Sancus11/RackGloves/images/IMG_20240603_130146942.jpg

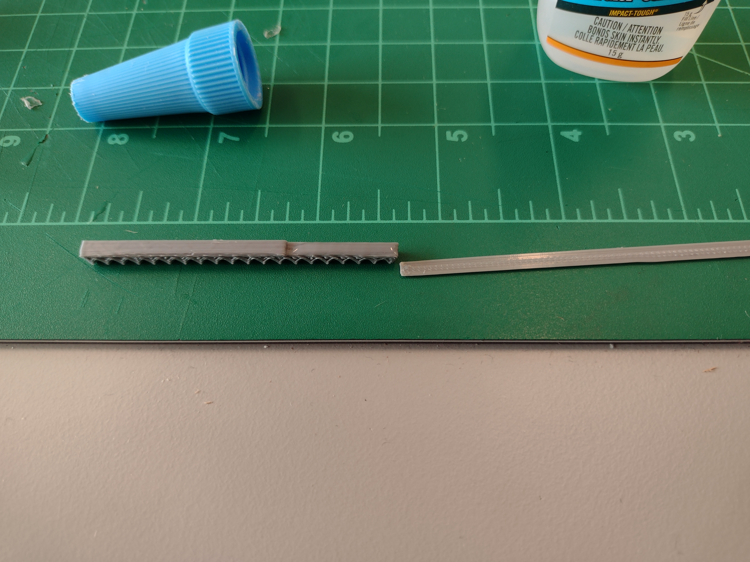
images/IMG_20240603_130146942.jpg
