Sancus11/RackGloves/images/IMG_20240604_150035656.jpg

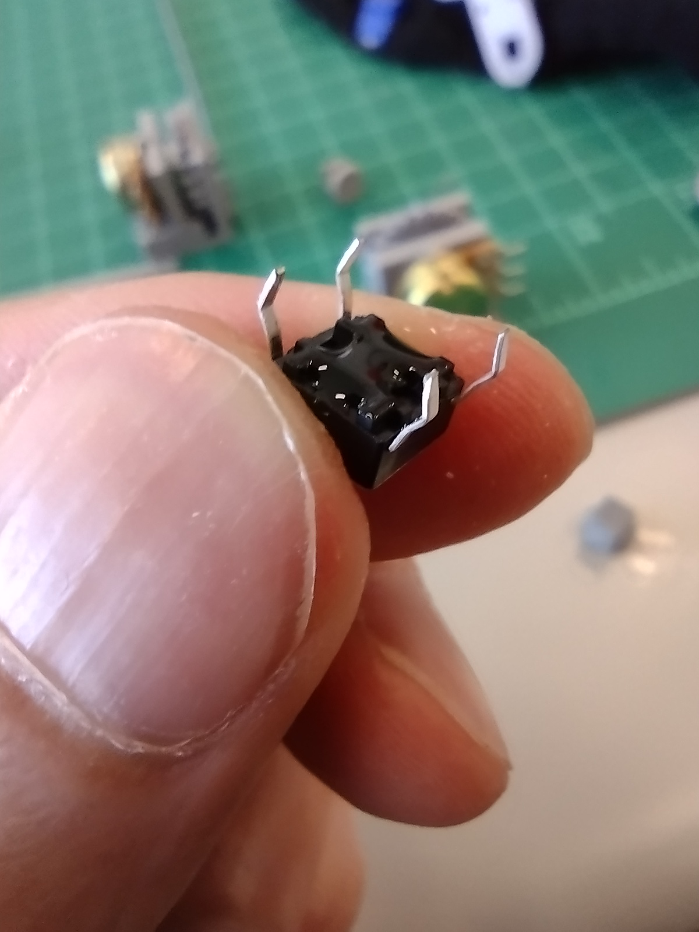
images/IMG_20240604_150035656.jpg
