Sancus11/RackGloves/images/IMG_20240606_152140470.jpg

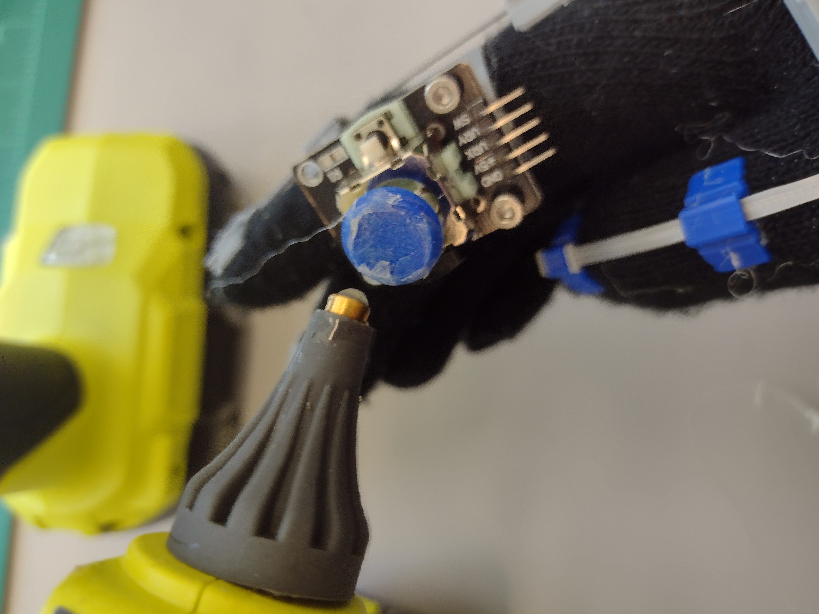
images/IMG_20240606_152140470.jpg
