Sancus11/RackGloves/everything v1/proto gloves/P-T-M-24-L.stl

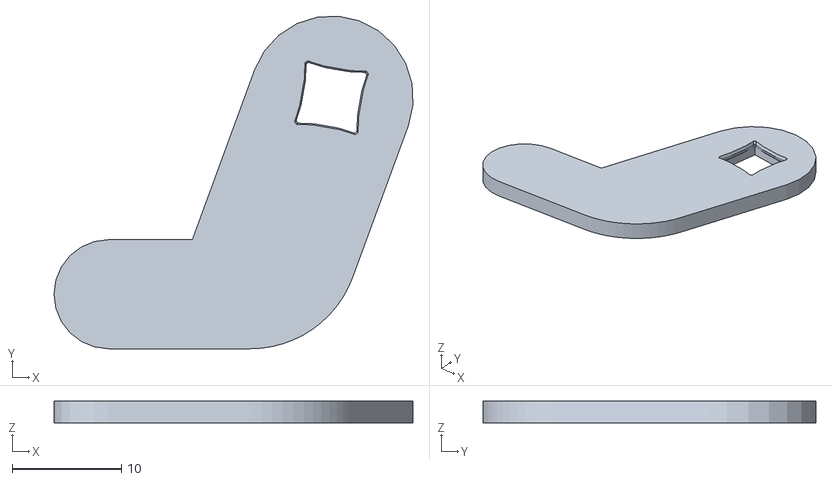
[picture p24: CAD file, 2024-06-14]
everything v1/proto gloves/P-T-M-24-L.stl
32.9 x 30.5 x 2.00
