Sancus11/RackGloves/everything v1/rack unit/spur gear.stl

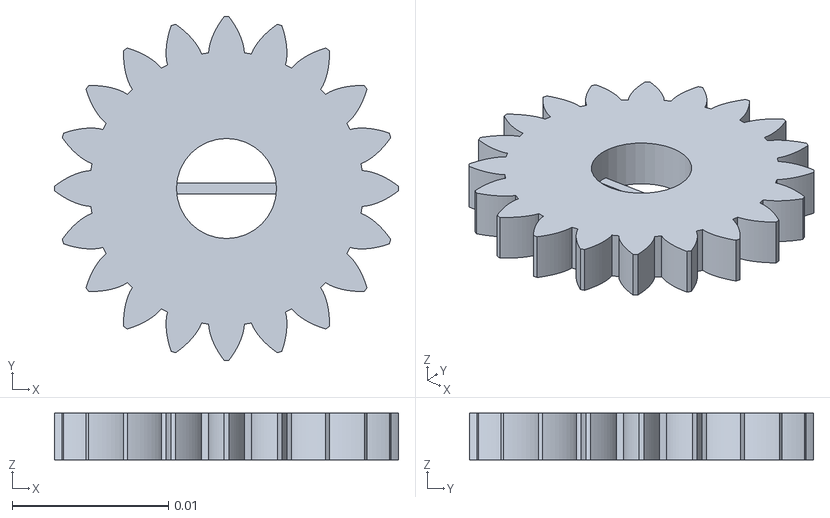
[picture p25: CAD file, 2024-06-14]
everything v1/rack unit/spur gear.stl
0.022 x 0.022 x 0.003
