Sancus11/RackGloves/everything v1/controlls/joystick nub.stl

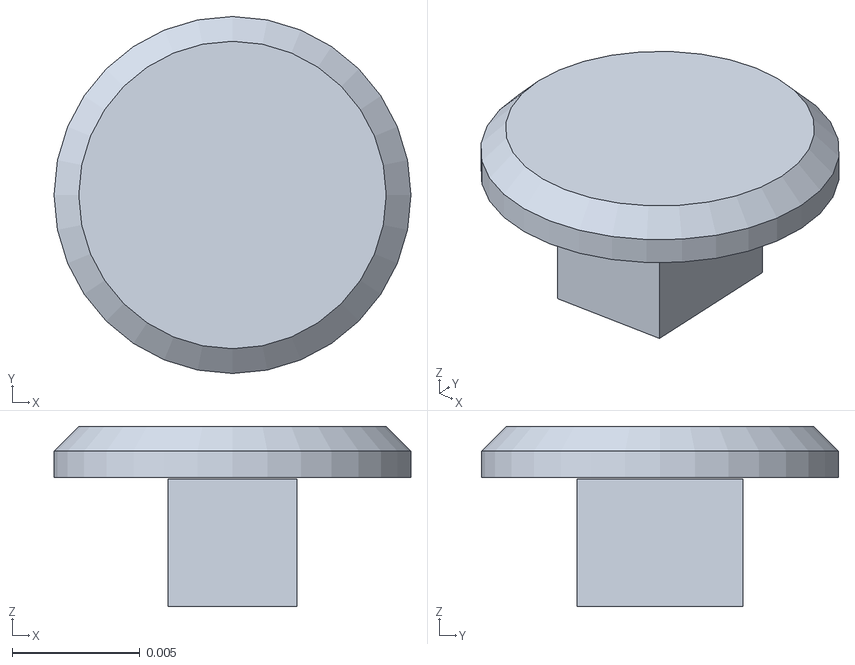
[picture p26: CAD file, 2024-06-14]
everything v1/controlls/joystick nub.stl
0.014 x 0.014 x 0.00707
