Sancus11/RackGloves/everything v1/espcase/button push.stl

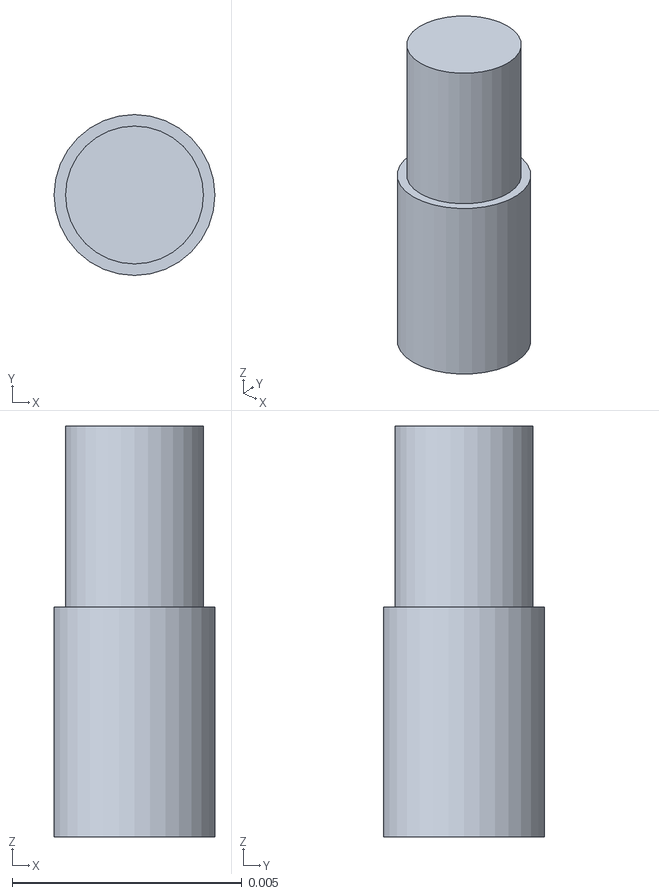
[picture p27: CAD file, 2024-06-14]
everything v1/espcase/button push.stl
0.0035 x 0.0035 x 0.00894
