Sancus11/RackGloves/everything v1/guides/glue guide m.stl

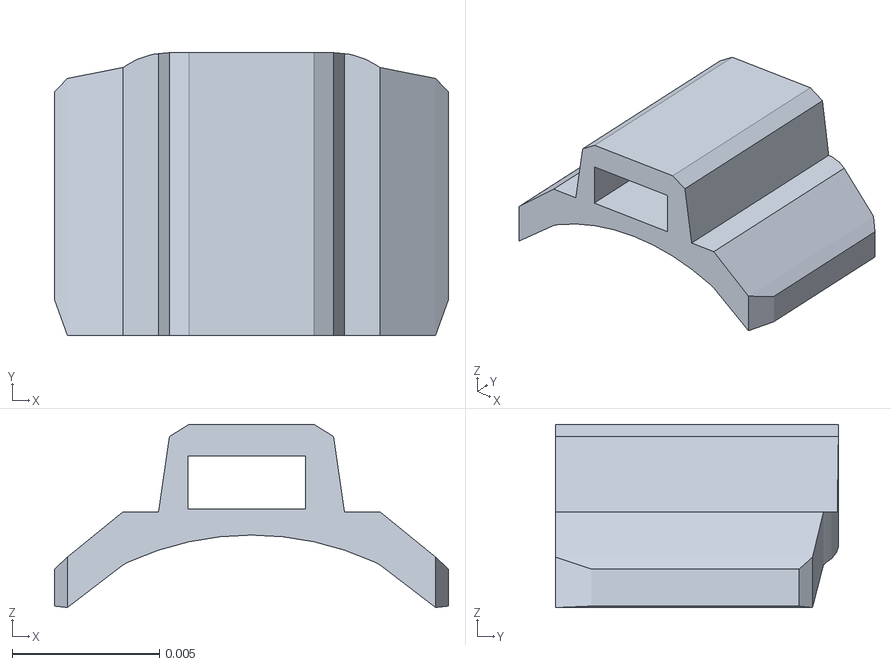
[picture p28: CAD file, 2024-06-14]
everything v1/guides/glue guide m.stl
0.0134 x 0.00961 x 0.00623
