Sancus11/RackGloves/everything v1/proto gloves/P-T-M modular/P-T-M-22-L.stl

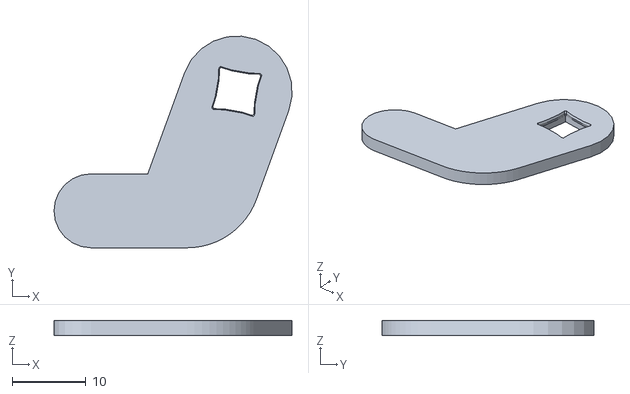
[picture p29: CAD file, 2024-06-14]
everything v1/proto gloves/P-T-M modular/P-T-M-22-L.stl
32.2 x 28.6 x 2.00
