Sancus11/RackGloves/everything v1/proto gloves/P-U-02-A.stl

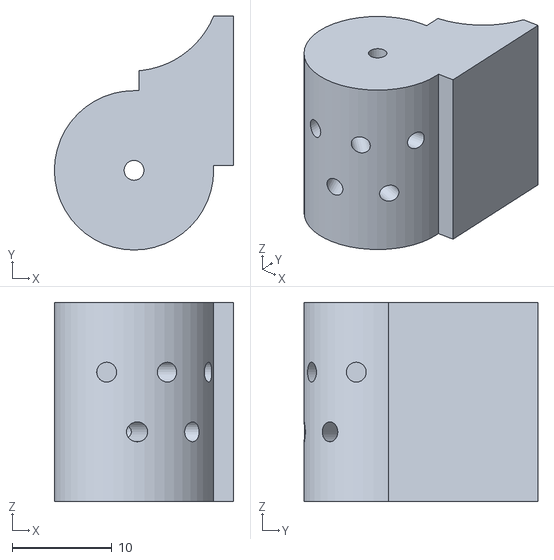
[picture p30: CAD file, 2024-06-14]
everything v1/proto gloves/P-U-02-A.stl
18.0 x 23.5 x 20.0
