Sancus11/RackGloves/everything v1/rack unit/fingerline.stl

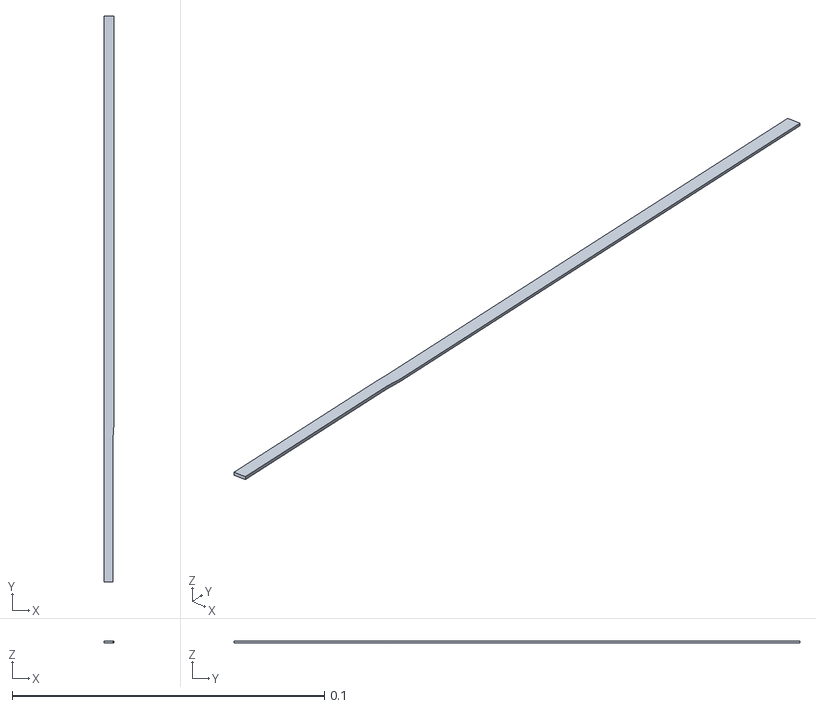
[picture p31: CAD file, 2024-06-14]
everything v1/rack unit/fingerline.stl
0.00316 x 0.181 x 0.0007
