Sancus11/RackGloves/everything v1/controlls/button baseplate.stl

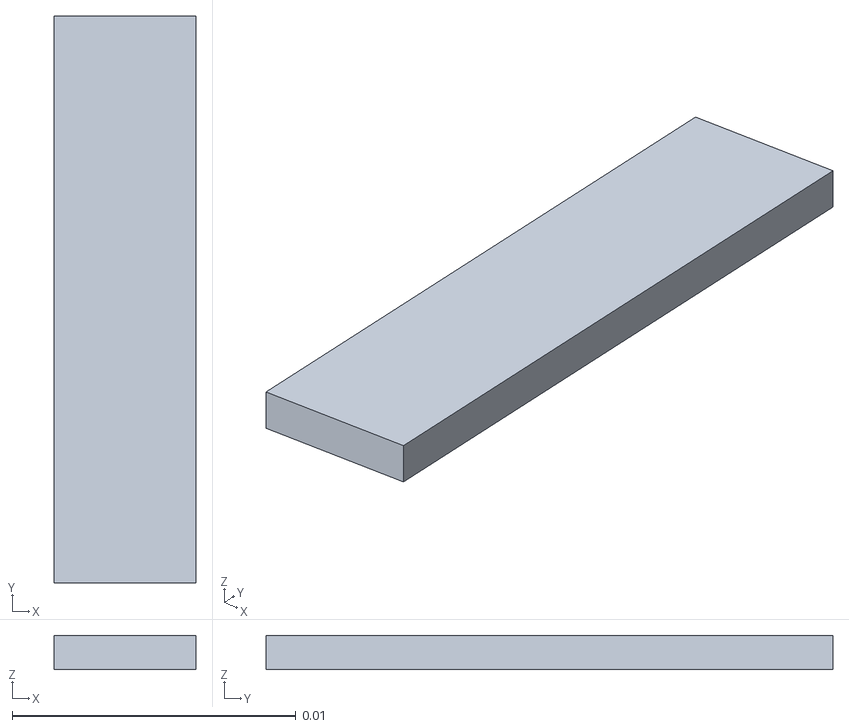
[picture p32: CAD file, 2024-06-14]
everything v1/controlls/button baseplate.stl
0.005 x 0.02 x 0.0012
