Sancus11/RackGloves/everything v1/guides/glue guide xl.stl

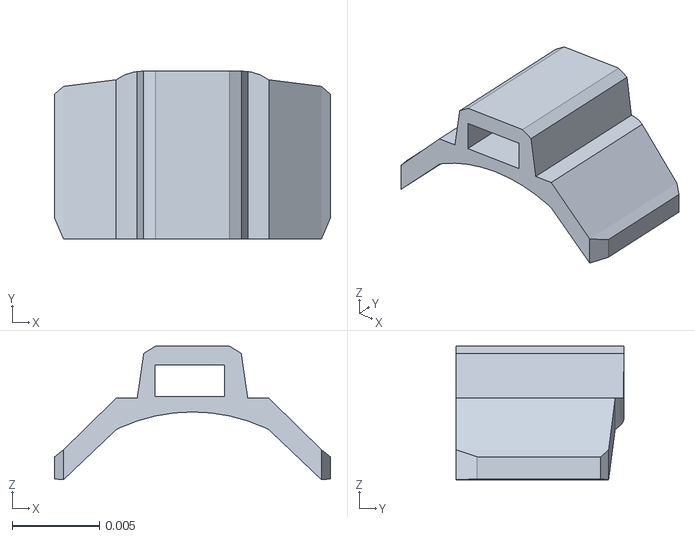
[picture p33: CAD file, 2024-06-14]
everything v1/guides/glue guide xl.stl
0.0158 x 0.00961 x 0.00764
