Sancus11/RackGloves/everything v1/proto gloves/P-T-M modular/P-T-M-18-R.stl

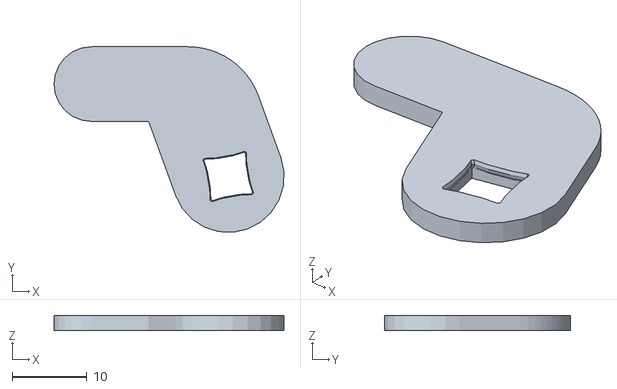
[picture p34: CAD file, 2024-06-14]
everything v1/proto gloves/P-T-M modular/P-T-M-18-R.stl
30.8 x 24.9 x 2.00
