Sancus11/RackGloves/everything v1/rack unit/rack.stl

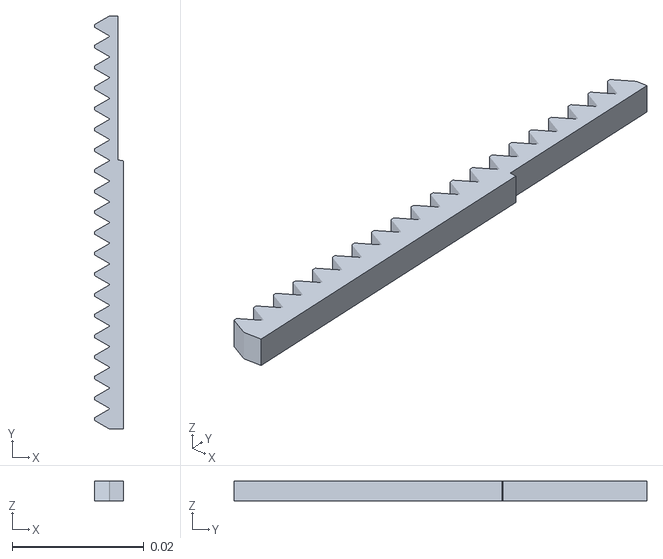
[picture p35: CAD file, 2024-06-14]
everything v1/rack unit/rack.stl
0.0044 x 0.0627 x 0.003
