Sancus11/RackGloves/everything v1/controlls/joystick mount.stl

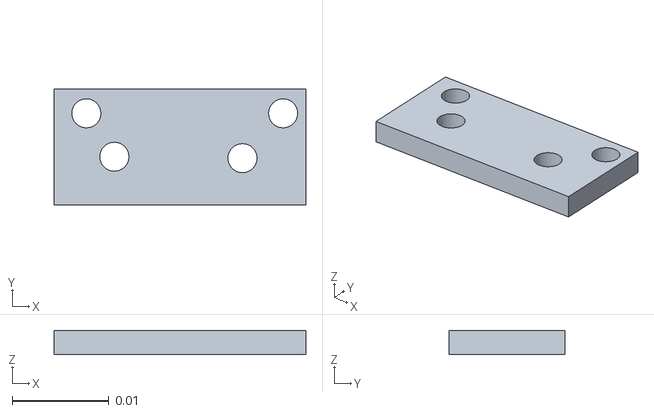
[picture p36: CAD file, 2024-06-14]
everything v1/controlls/joystick mount.stl
0.026 x 0.012 x 0.0025
