Sancus11/RackGloves/everything v1/guides/glue guide s.stl

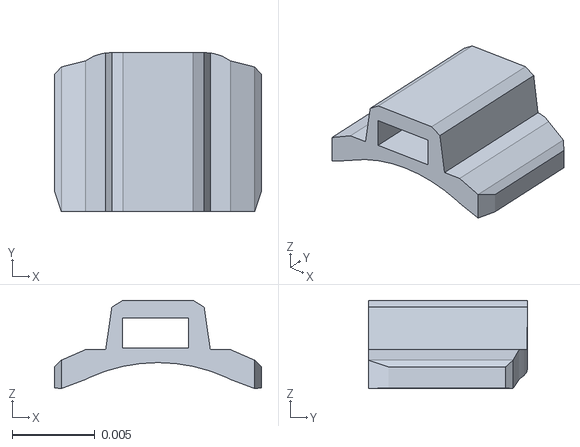
[picture p37: CAD file, 2024-06-14]
everything v1/guides/glue guide s.stl
0.0125 x 0.00961 x 0.00533
