Sancus11/RackGloves/everything v1/proto gloves/P-B-5-B-G- glued/P-B-5-B-G-07-L.stl

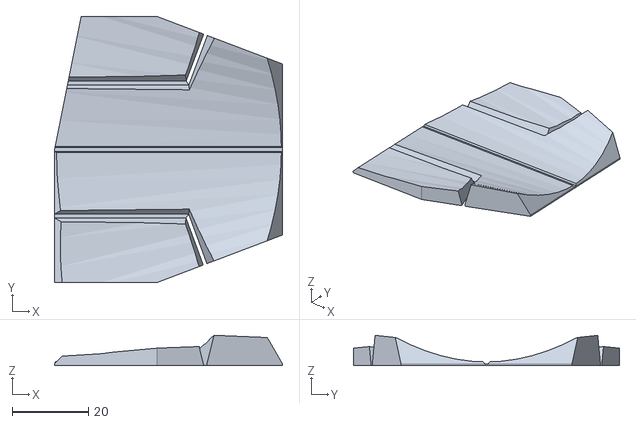
[picture p38: CAD file, 2024-06-14]
everything v1/proto gloves/P-B-5-B-G- glued/P-B-5-B-G-07-L.stl
60.0 x 70.0 x 8.00
