Sancus11/RackGloves/everything v1/proto gloves/P-R-B-1-A single point.stl

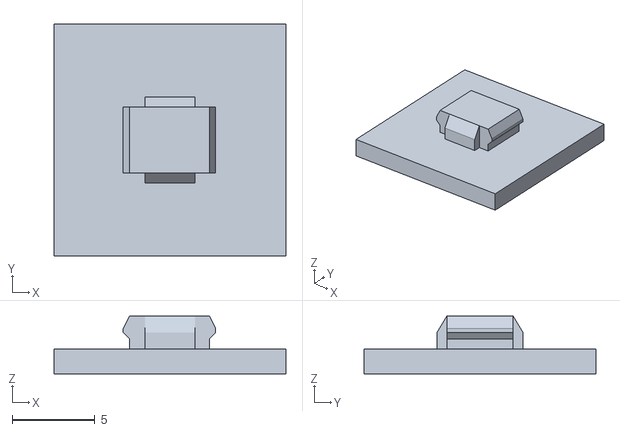
[picture p39: CAD file, 2024-06-14]
everything v1/proto gloves/P-R-B-1-A single point.stl
14.0 x 14.0 x 3.50
