Sancus11/RackGloves/everything v1/proto gloves/P-B-5-B-G- glued/P-B-5-B-G-05-R.stl

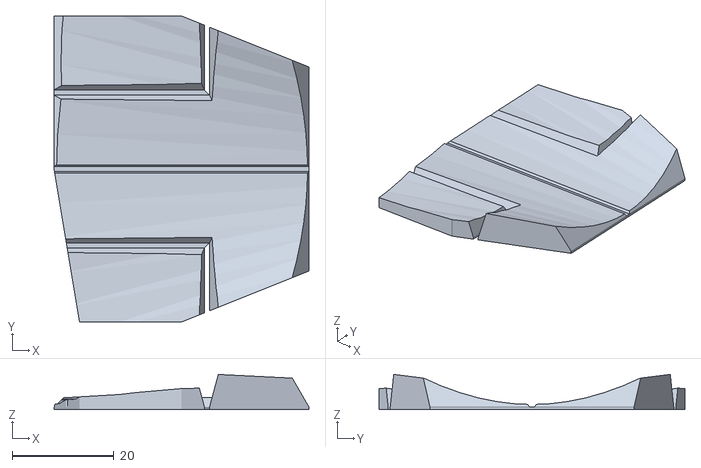
[picture p40: CAD file, 2024-06-14]
everything v1/proto gloves/P-B-5-B-G- glued/P-B-5-B-G-05-R.stl
50.0 x 60.0 x 6.89
