Sancus11/RackGloves/everything v1/proto gloves/P-B-5-B-M- modular/P-B-5-B-M-05-L.stl

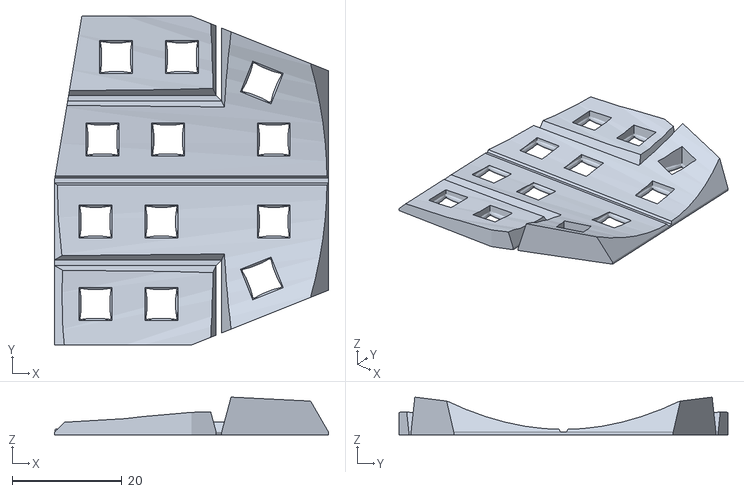
[picture p41: CAD file, 2024-06-14]
everything v1/proto gloves/P-B-5-B-M- modular/P-B-5-B-M-05-L.stl
50.0 x 60.0 x 6.89
