Sancus11/RackGloves/everything v1/proto gloves/P-T-M modular/P-T-M-28-L.stl

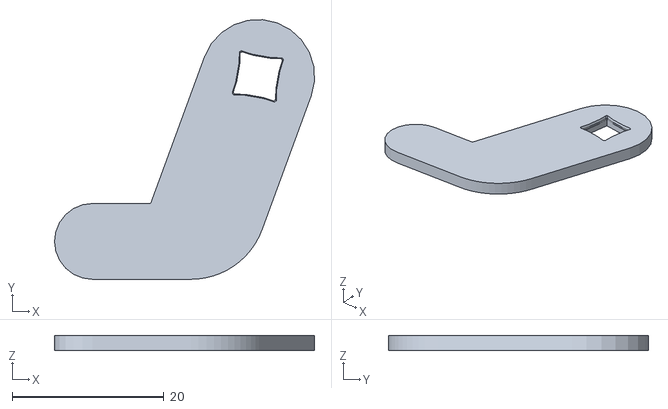
[picture p42: CAD file, 2024-06-14]
everything v1/proto gloves/P-T-M modular/P-T-M-28-L.stl
34.3 x 34.2 x 2.00
