Sancus11/RackGloves/everything v1/proto gloves/P-T-M modular/P-T-M-32-L.stl

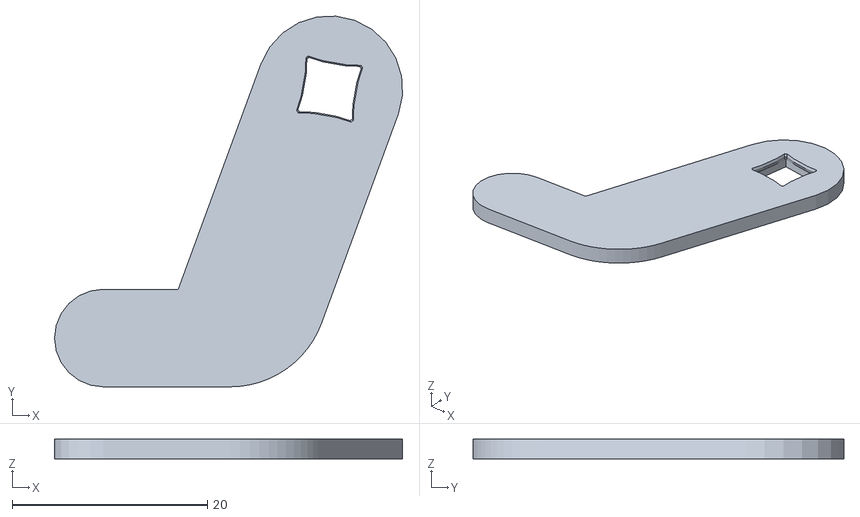
[picture p43: CAD file, 2024-06-14]
everything v1/proto gloves/P-T-M modular/P-T-M-32-L.stl
35.7 x 38.0 x 2.00
