Sancus11/RackGloves/everything v1/proto gloves/P-T-M modular/P-T-M-20-L.stl

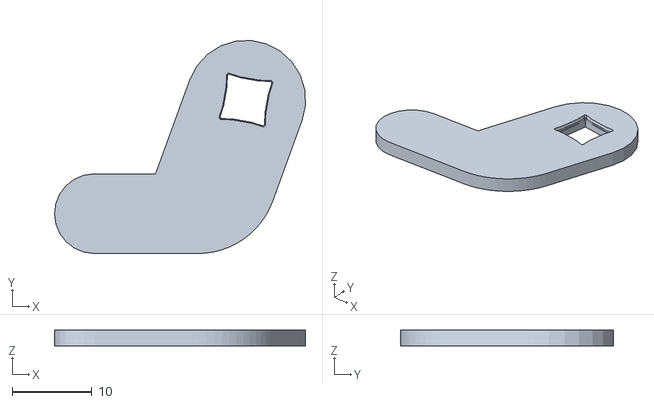
[picture p44: CAD file, 2024-06-14]
everything v1/proto gloves/P-T-M modular/P-T-M-20-L.stl
31.5 x 26.7 x 2.00
