Sancus11/RackGloves/everything v1/proto gloves/P-T-M modular/P-T-M-14-R.stl

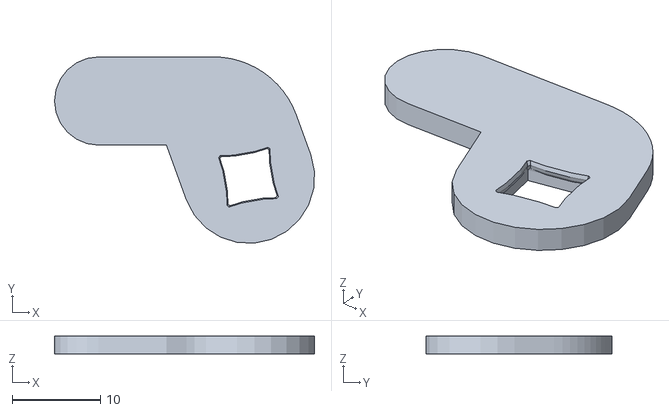
[picture p45: CAD file, 2024-06-14]
everything v1/proto gloves/P-T-M modular/P-T-M-14-R.stl
29.4 x 21.1 x 2.00
