Sancus11/RackGloves/everything v1/proto gloves/P-T-M modular/P-T-M-30-R.stl

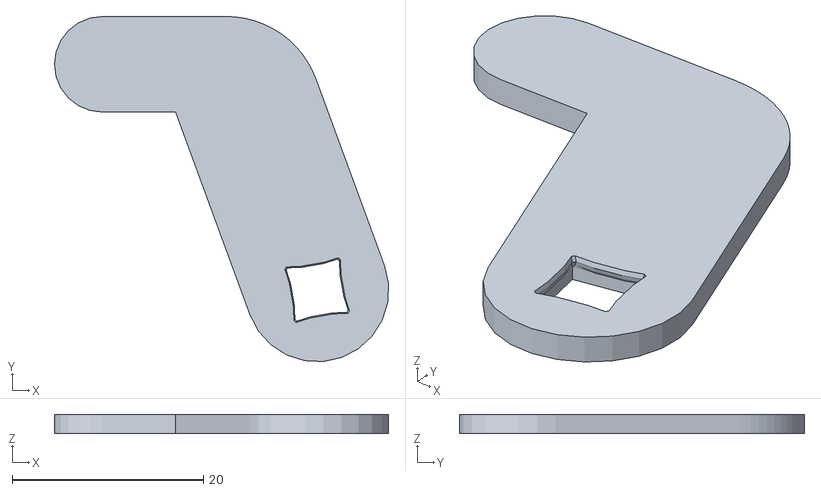
[picture p46: CAD file, 2024-06-14]
everything v1/proto gloves/P-T-M modular/P-T-M-30-R.stl
35.0 x 36.1 x 2.00
