Sancus11/RackGloves/everything v1/proto gloves/P-T-M modular/P-T-M-26-L.stl

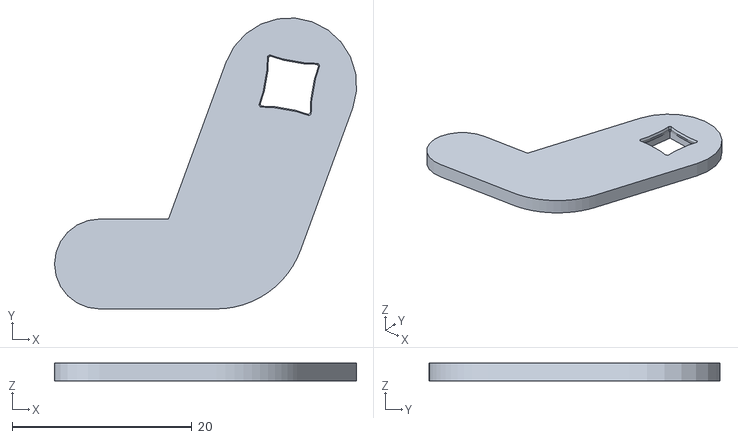
[picture p47: CAD file, 2024-06-14]
everything v1/proto gloves/P-T-M modular/P-T-M-26-L.stl
33.6 x 32.4 x 2.00
