Sancus11/RackGloves/images/IMG_20240603_131628712.jpg

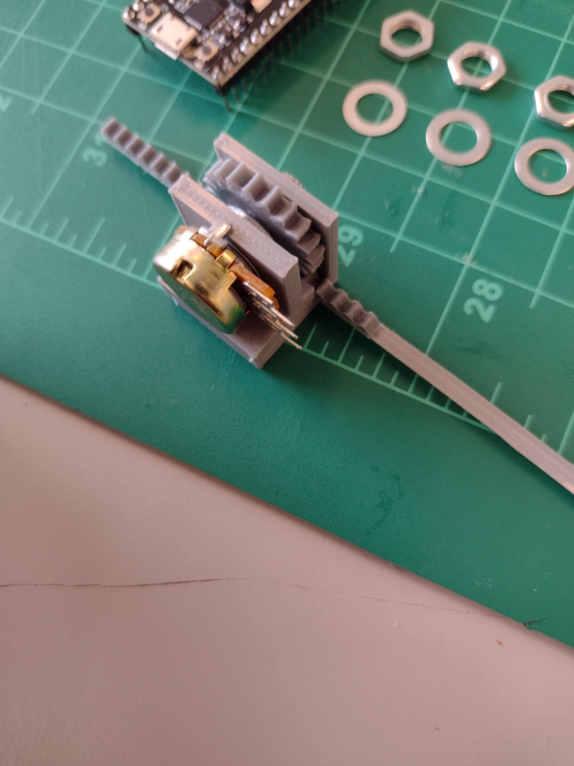
images/IMG_20240603_131628712.jpg
