Sancus11/RackGloves/images/IMG_20240604_143251174.jpg

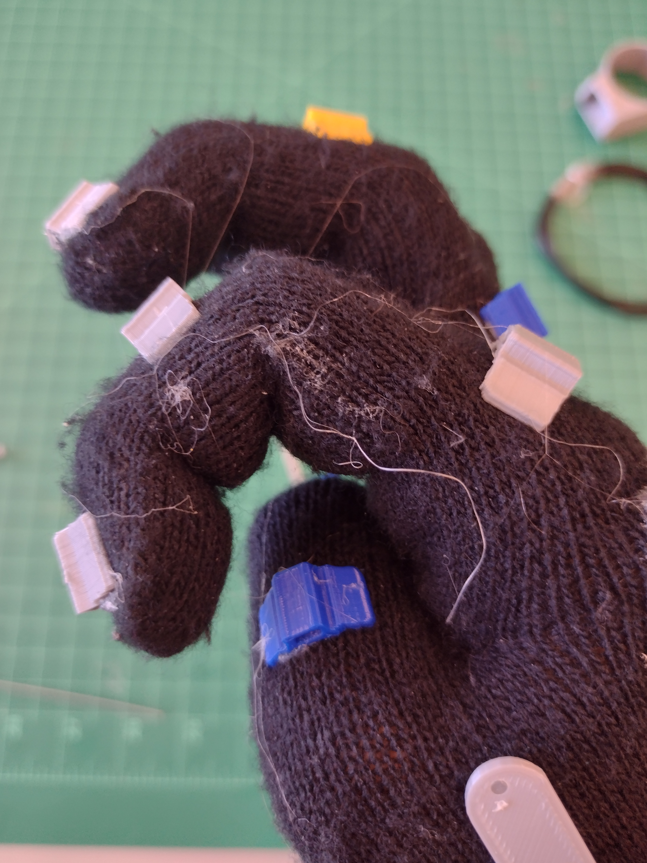
images/IMG_20240604_143251174.jpg
