Sancus11/RackGloves/images/IMG_20240607_115500967.jpg

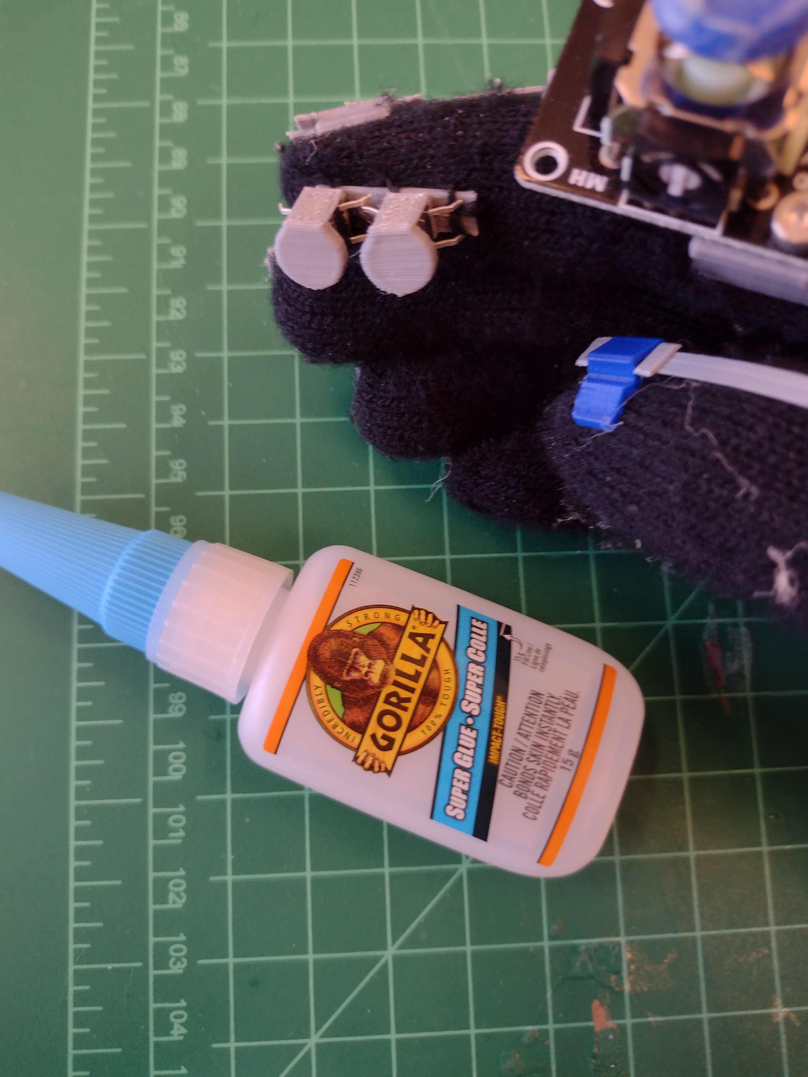
images/IMG_20240607_115500967.jpg
