Sancus11/RackGloves/images/IMG_20240610_132420437.jpg

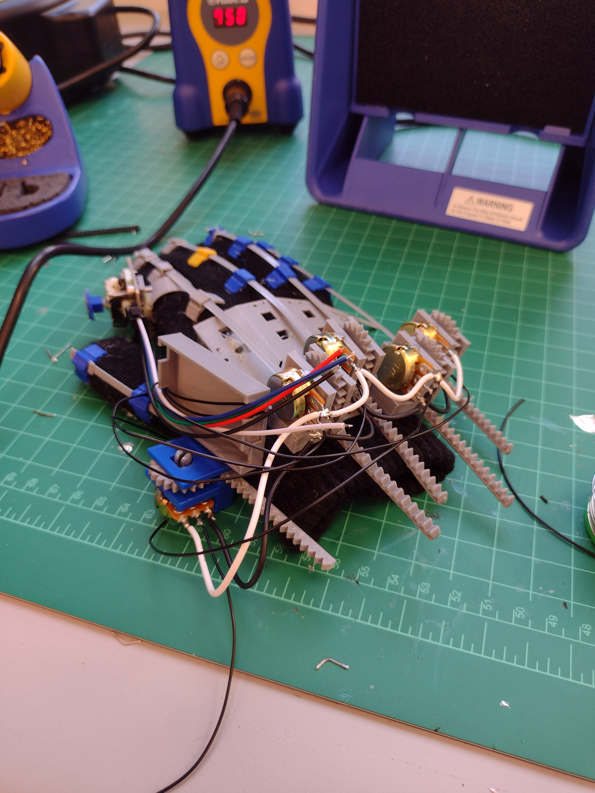
images/IMG_20240610_132420437.jpg
