Sancus11/RackGloves/images/IMG_20240611_144900195.jpg

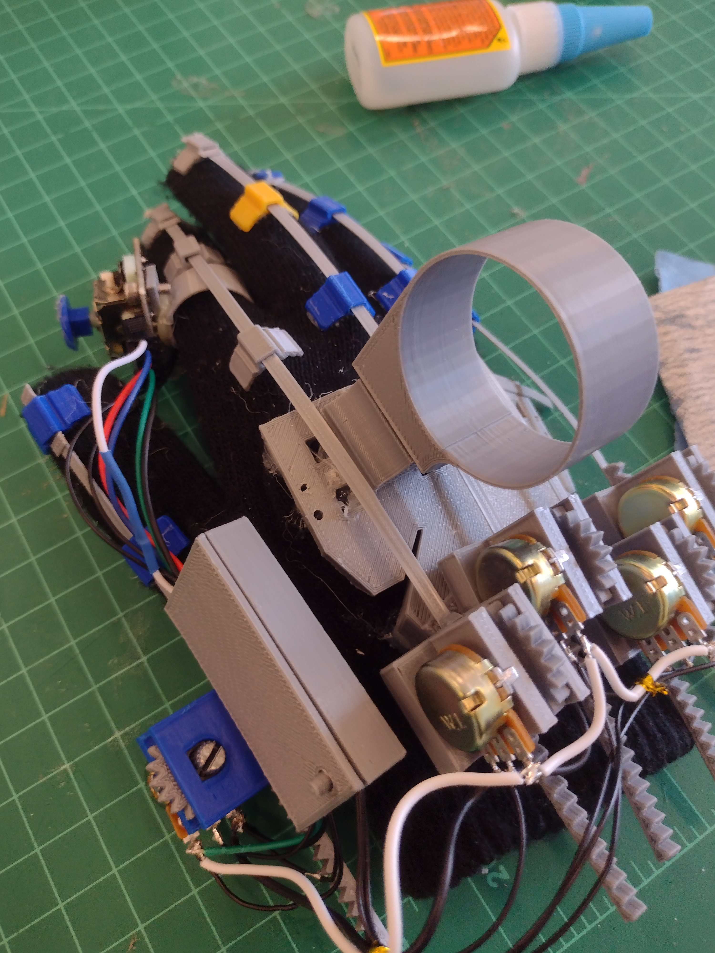
images/IMG_20240611_144900195.jpg
